ElyesKhechine/i-cowcare-iot-health-monitoring/Project_Presentation/Resources/Images/acceleration_chart.jpg

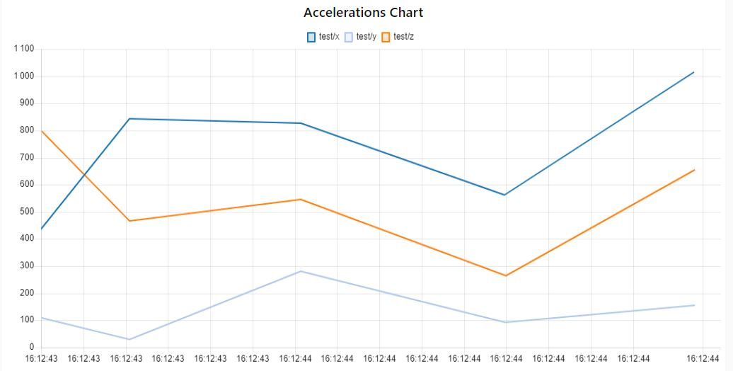
Project_Presentation/Resources/Images/acceleration_chart.jpg
