ElyesKhechine/i-cowcare-iot-health-monitoring/Project_Presentation/Resources/Images/battery_life_estimation.jpg

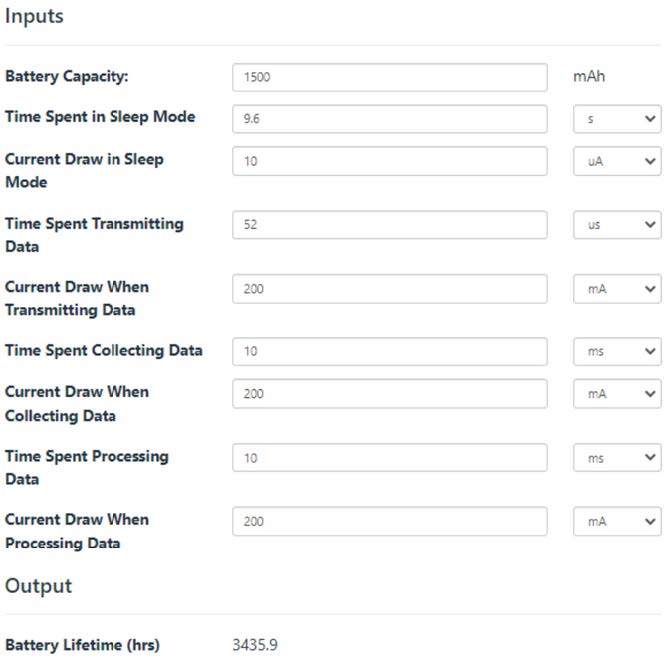
Project_Presentation/Resources/Images/battery_life_estimation.jpg
