ElyesKhechine/i-cowcare-iot-health-monitoring/Project_Presentation/Resources/Images/CSV_file.png

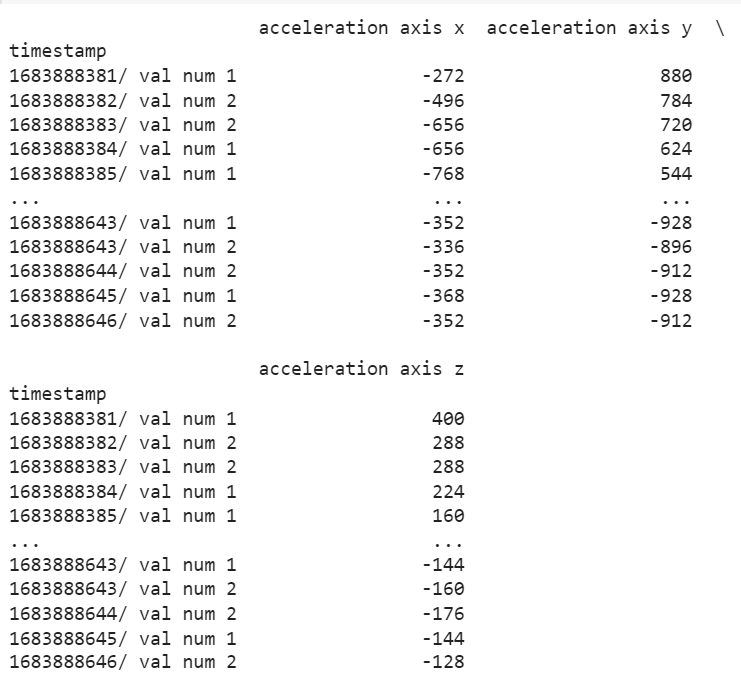
Project_Presentation/Resources/Images/CSV_file.png
