ElyesKhechine/i-cowcare-iot-health-monitoring/Project_Presentation/Resources/Images/nn_classifier_edgeimpulse.png

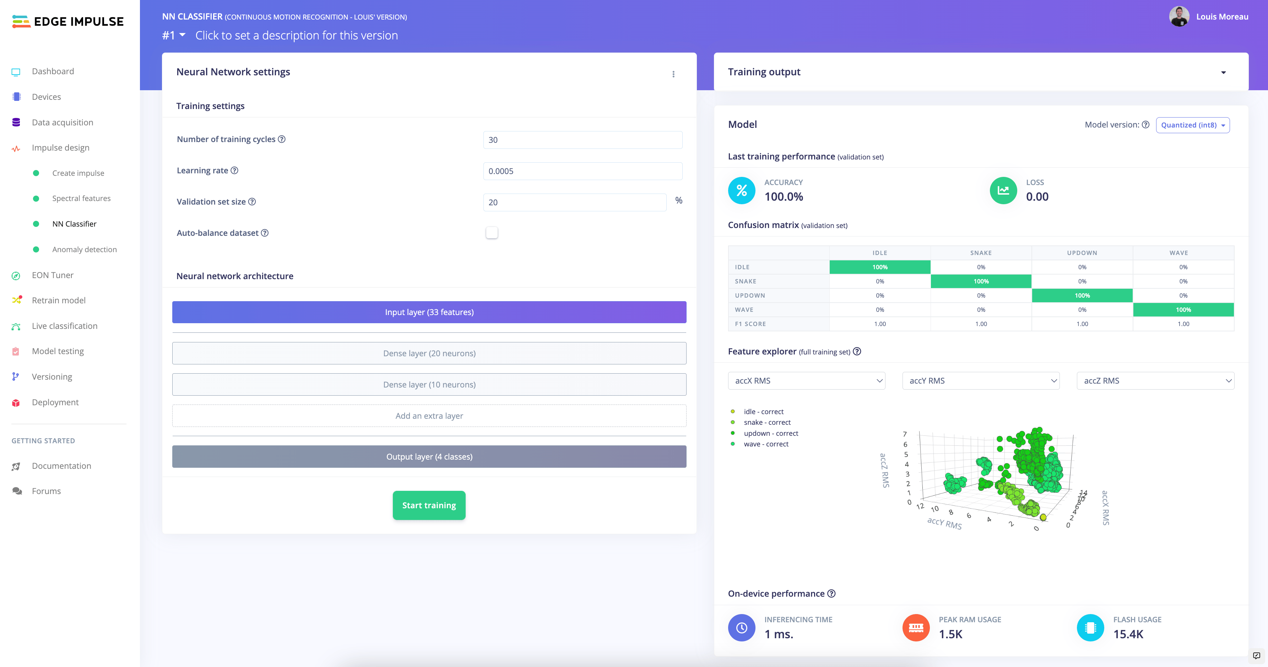
Project_Presentation/Resources/Images/nn_classifier_edgeimpulse.png
