ElyesKhechine/i-cowcare-iot-health-monitoring/Project_Presentation/Resources/Images/node-red_temperature_gauges.jpg

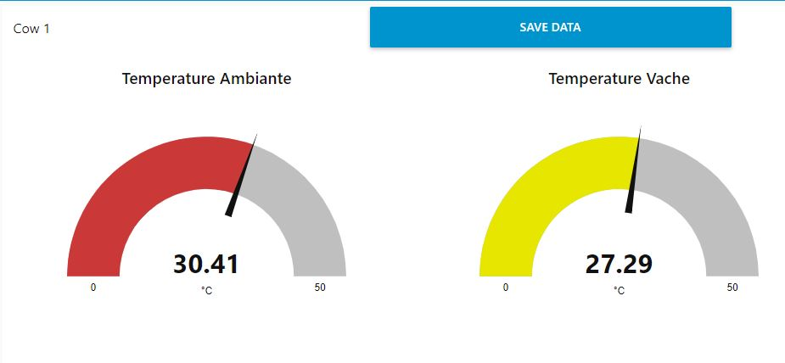
Project_Presentation/Resources/Images/node-red_temperature_gauges.jpg
