ElyesKhechine/i-cowcare-iot-health-monitoring/src/3D_Design/STL_files/CR_123A_Battery_Holder_I-CowCare_PFA_2022-2023.STL

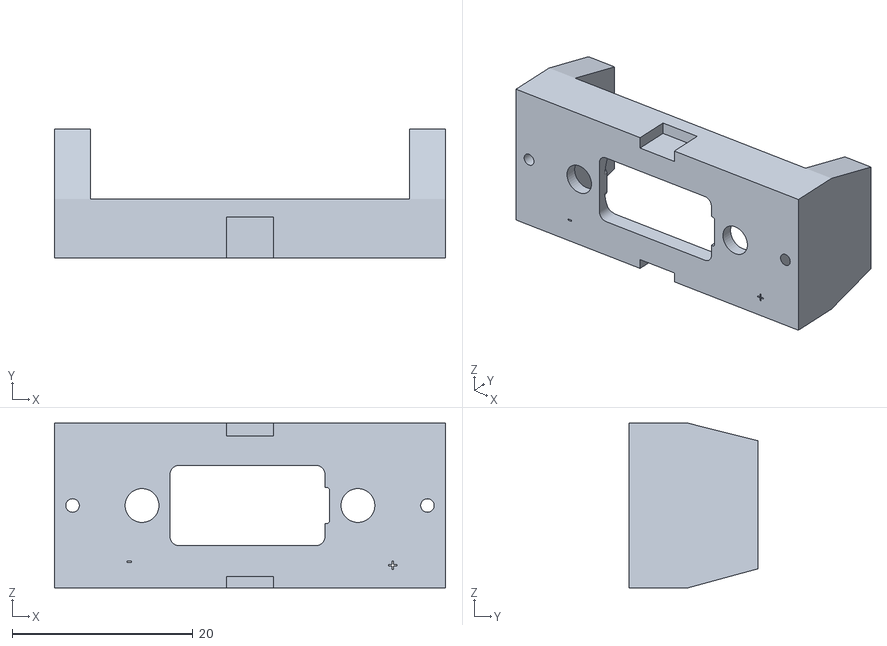
[picture p62: CAD file, 2023-11-28]
src/3D_Design/STL_files/CR_123A_Battery_Holder_I-CowCare_PFA_2022-2023.STL
43.3 x 14.2 x 18.2
