ElyesKhechine/i-cowcare-iot-health-monitoring/src/3D_Design/SOLIDWORKS_Assembly/CR_123A_Battery_I-CowCare_PFA_2022-2023.SLDPRT

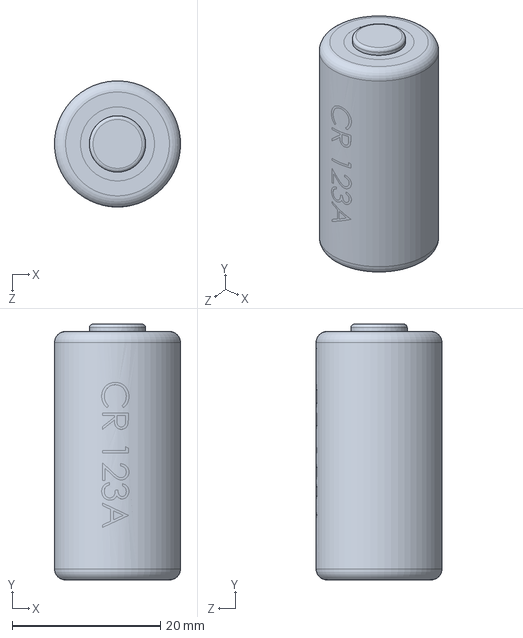
[picture p63: CAD file, 2023-11-28]
src/3D_Design/SOLIDWORKS_Assembly/CR_123A_Battery_I-CowCare_PFA_2022-2023.SLDPRT
17.0 x 34.5 x 17.0 mm
