ElyesKhechine/i-cowcare-iot-health-monitoring/src/3D_Design/Resources/PATM-1240_B.STL

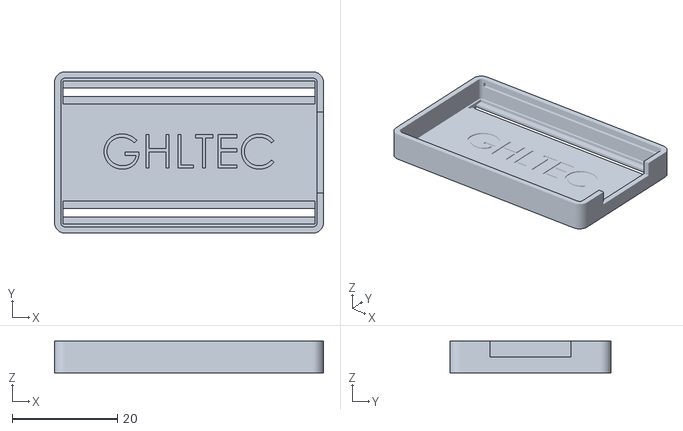
[picture p64: CAD file, 2023-11-28]
src/3D_Design/Resources/PATM-1240_B.STL
51.0 x 30.6 x 6.00
