ElyesKhechine/i-cowcare-iot-health-monitoring/src/3D_Design/Resources/CR123A  Battery Holder.step

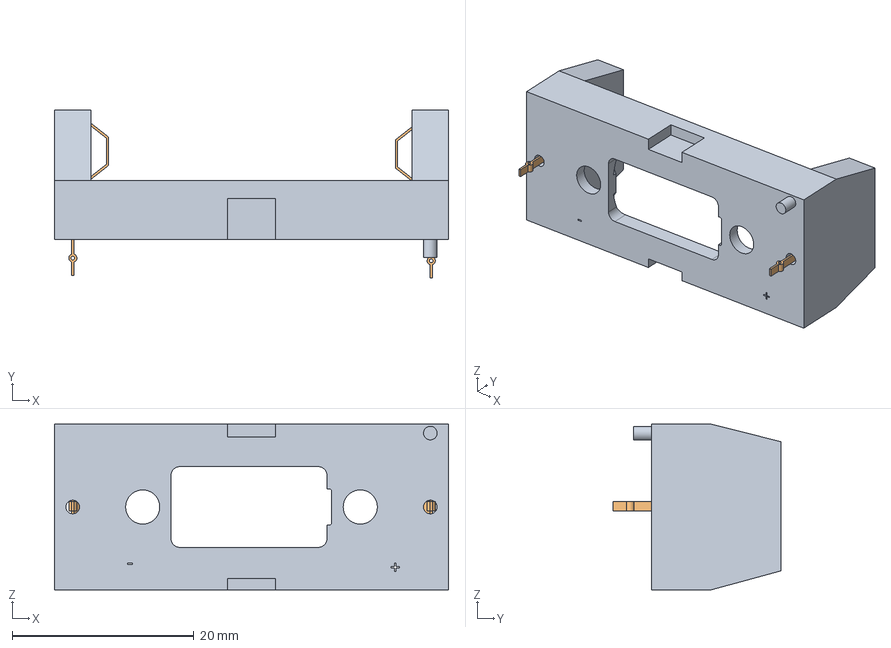
[picture p65: CAD file, 2023-11-28]
src/3D_Design/SOLIDWORKS_Assembly/CR123A Battery Holder.step
43.3 x 18.5 x 18.2 mm
