ElyesKhechine/i-cowcare-iot-health-monitoring/src/3D_Design/Resources/Holder 3D.STEP

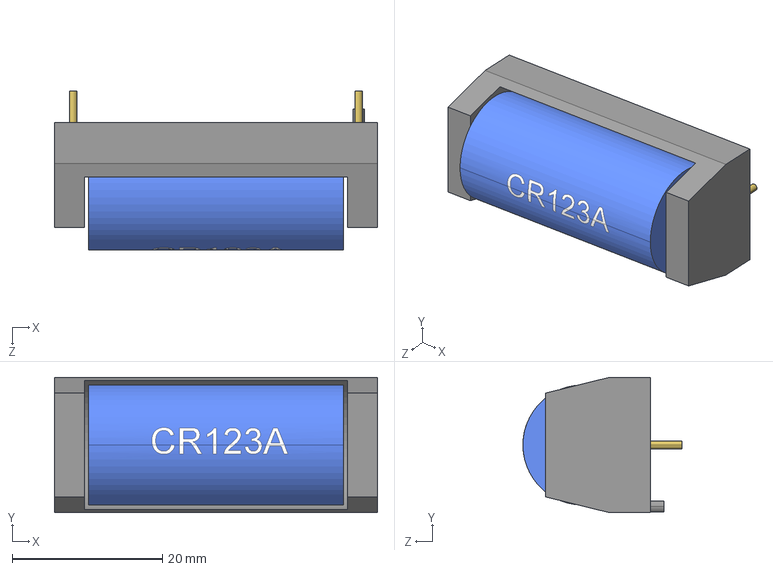
[picture p66: CAD file, 2023-11-28]
src/3D_Design/Resources/Holder 3D.STEP
43.0 x 18.0 x 21.2 mm
