ElyesKhechine/i-cowcare-iot-health-monitoring/src/3D_Design/SOLIDWORKS_Assembly/Collier_I-CowCare_PFA_2022-2023.SLDPRT

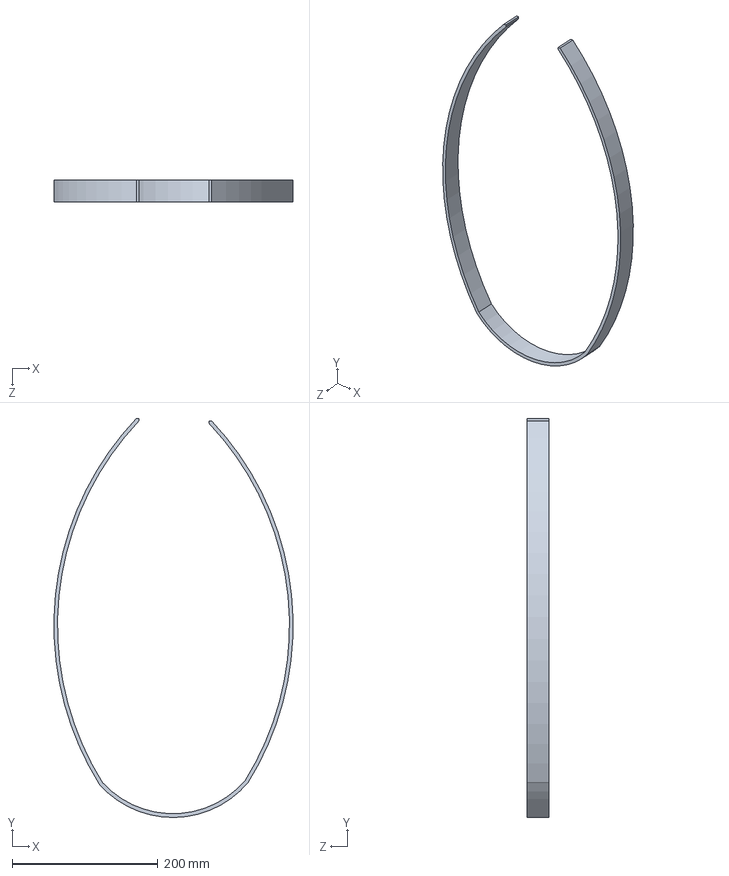
[picture p67: CAD file, 2023-11-28]
src/3D_Design/SOLIDWORKS_Assembly/Collier_I-CowCare_PFA_2022-2023.SLDPRT
328.1 x 547.8 x 30.0 mm
