ElyesKhechine/i-cowcare-iot-health-monitoring/src/3D_Design/Resources/D7 - TC (D7)-1.STL

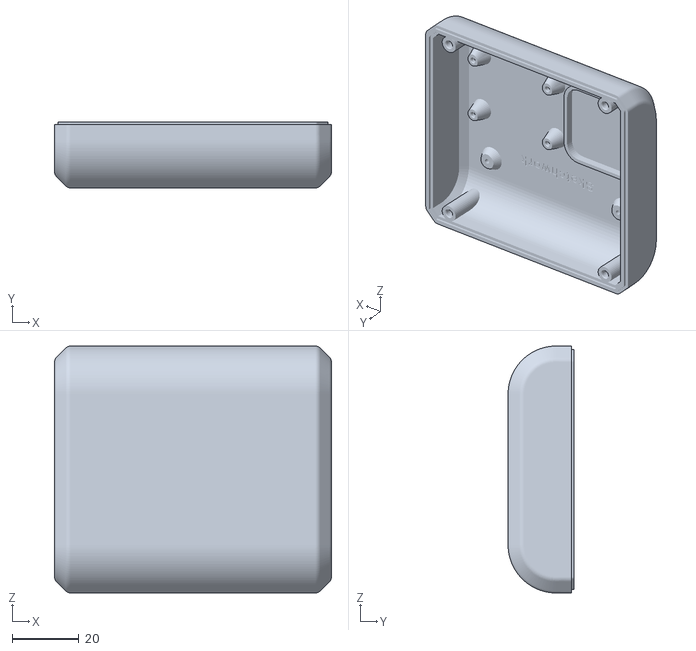
[picture p68: CAD file, 2023-11-28]
src/3D_Design/Resources/D7 - TC (D7)-1.STL
83.0 x 19.8 x 74.0
