ElyesKhechine/i-cowcare-iot-health-monitoring/src/3D_Design/SOLIDWORKS_Assembly/Accelerometer_ADXL377Z_I-CowCare_PFA_2022-2023.SLDPRT

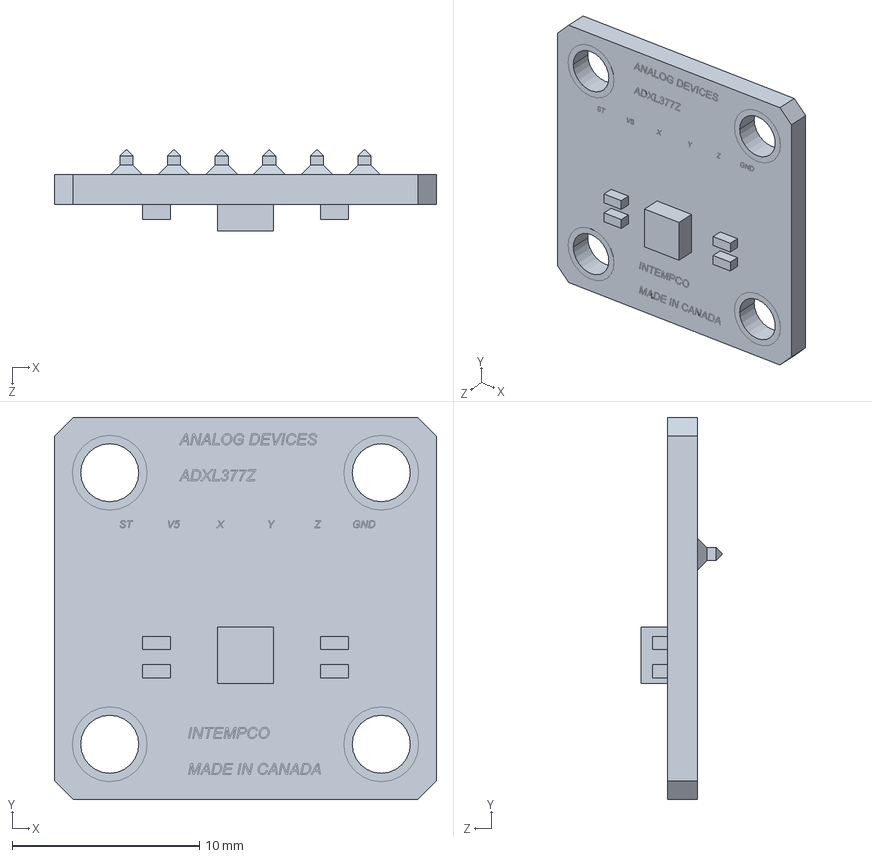
[picture p69: CAD file, 2023-11-28]
src/3D_Design/SOLIDWORKS_Assembly/Accelerometer_ADXL377Z_I-CowCare_PFA_2022-2023.SLDPRT
20.4 x 20.4 x 4.30 mm
