ElyesKhechine/i-cowcare-iot-health-monitoring/src/3D_Design/Resources/D7 - BC (D7)-1.STL

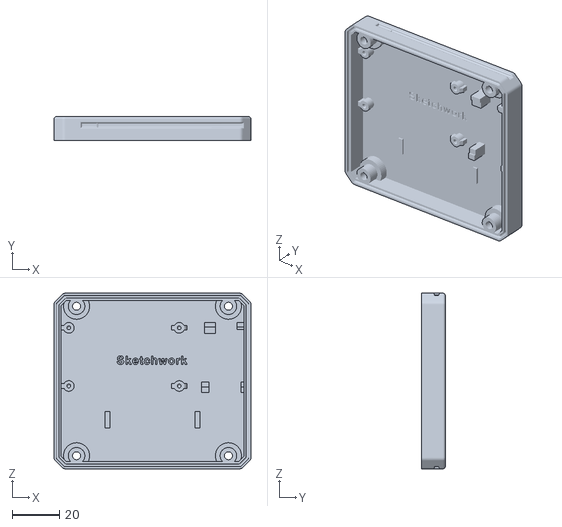
[picture p70: CAD file, 2023-11-28]
src/3D_Design/Resources/D7 - BC (D7)-1.STL
83.0 x 10.00 x 74.0
