ElyesKhechine/i-cowcare-iot-health-monitoring/src/MQTT/mqtt_I-CowCare_PFA_22-23.h

#ifndef MQTT_H
#define MQTT_H
#include <Arduino.h>
#define MSG_BUFFER_SIZE (50)
void setup_wifi();
void reconnect();
void callback(char* topic, byte* payload, unsigned int length);
void publishMessage(const char* topic, String payload , boolean retained);
unsigned long getTime();


/****** root certificate *********/
// this certificate is used for authentification
static const char *root_ca PROGMEM = R"EOF(
-----BEGIN CERTIFICATE-----
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
-----END CERTIFICATE-----
)EOF";
#endif
